thesunRider/cuBo/assets/rnd3.png

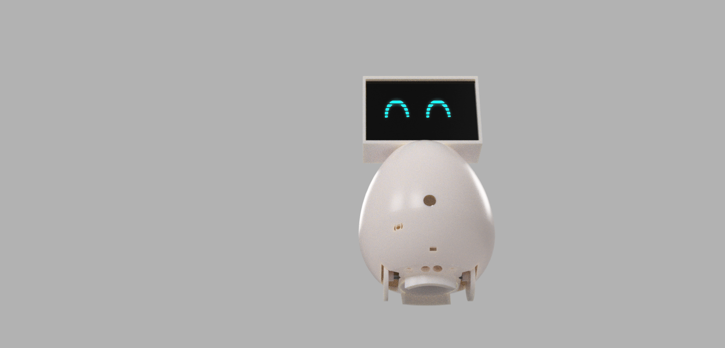
assets/rnd3.png
