thesunRider/cuBo/code/test/arduino/tof/tof.ino

#include <Wire.h>
#include <vl53lx_class.h>


#define DEV_I2C Wire
#define SerialPort Serial

#ifndef LED_BUILTIN
#define LED_BUILTIN 13
#endif
#define LedPin LED_BUILTIN

// Components.
VL53LX sensor_vl53lx_sat(&DEV_I2C, A1);


/* Setup ---------------------------------------------------------------------*/

void setup()
{
   // Led.
   pinMode(LedPin, OUTPUT);

   // Initialize serial for output.
   SerialPort.begin(115200);
   SerialPort.println("Starting...");

   // Initialize I2C bus.
   DEV_I2C.begin();

   // Configure VL53LX satellite component.
   sensor_vl53lx_sat.begin();

   // Switch off VL53LX satellite component.
   sensor_vl53lx_sat.VL53LX_Off();

   //Initialize VL53LX satellite component.
   sensor_vl53lx_sat.InitSensor(0x12);

   // Start Measurements
   sensor_vl53lx_sat.VL53LX_StartMeasurement();
}

void loop()
{
   VL53LX_MultiRangingData_t MultiRangingData;
   VL53LX_MultiRangingData_t *pMultiRangingData = &MultiRangingData;
   uint8_t NewDataReady = 0;
   int no_of_object_found = 0, j;
   char report[64];
   int status;

   do
   {
      status = sensor_vl53lx_sat.VL53LX_GetMeasurementDataReady(&NewDataReady);
   } while (!NewDataReady);

   //Led on
   digitalWrite(LedPin, HIGH);

   if((!status)&&(NewDataReady!=0))
   {
      status = sensor_vl53lx_sat.VL53LX_GetMultiRangingData(pMultiRangingData);
      no_of_object_found=pMultiRangingData->NumberOfObjectsFound;
      snprintf(report, sizeof(report), "VL53LX Satellite: Count=%d, #Objs=%1d ", pMultiRangingData->StreamCount, no_of_object_found);
      SerialPort.print(report);
      for(j=0;j<no_of_object_found;j++)
      {
         if(j!=0)SerialPort.print("\r\n                               ");
         SerialPort.print("status=");
         SerialPort.print(pMultiRangingData->RangeData[j].RangeStatus);
         SerialPort.print(", D=");
         SerialPort.print(pMultiRangingData->RangeData[j].RangeMilliMeter);
         SerialPort.print("mm");
         SerialPort.print(", Signal=");
         SerialPort.print((float)pMultiRangingData->RangeData[j].SignalRateRtnMegaCps/65536.0);
         SerialPort.print(" Mcps, Ambient=");
         SerialPort.print((float)pMultiRangingData->RangeData[j].AmbientRateRtnMegaCps/65536.0);
         SerialPort.print(" Mcps");
      }
      SerialPort.println("");
      if (status==0)
      {
         status = sensor_vl53lx_sat.VL53LX_ClearInterruptAndStartMeasurement();
      }
   }

   digitalWrite(LedPin, LOW);
}
